DavidVentura/PicoPico/tests/data/hello_world.png

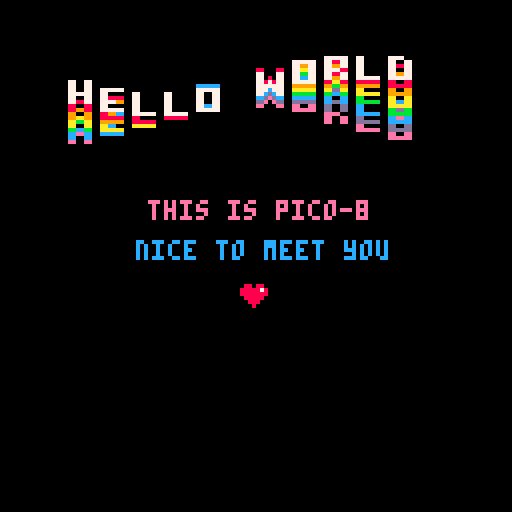
tests/data/hello_world.png
