DavidVentura/PicoPico/tests/data/menu.png

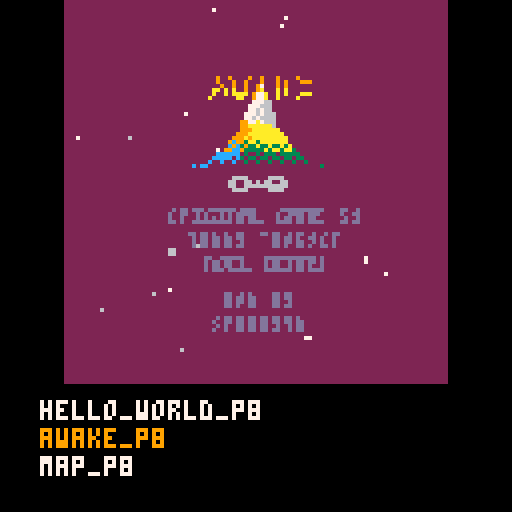
tests/data/menu.png
