DavidVentura/PicoPico/tests/data/test_basic_gfx.png

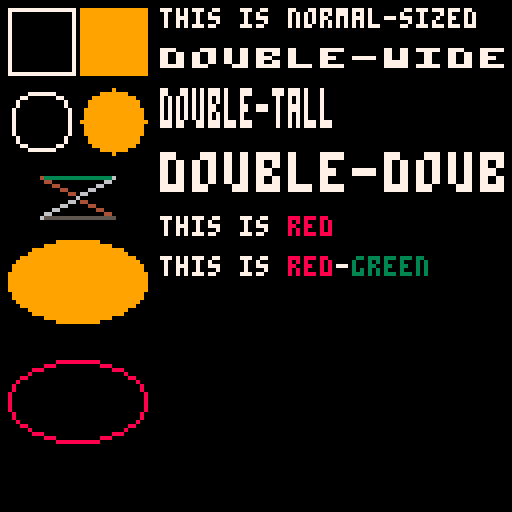
tests/data/test_basic_gfx.png
