DavidVentura/PicoPico/src/test_backend.c

bool init_video() {
    return 0;
}
void video_close() {}
void draw_hud() {};
void gfx_flip() {};
void delay(uint16_t ms) {};
uint32_t now() {
    return 1;
}
bool init_audio() {
    return false;
}
bool init_platform() {
    return false;
}

uint8_t current_hour() {
    return 0;
}
uint8_t current_minute() {
    return 0;
}
uint8_t wifi_strength() {
    return 0;
}
uint8_t battery_left() {
    return 0;
}
